sardus1970/JR_BLE_Gamepad/data/stripboard_top.png

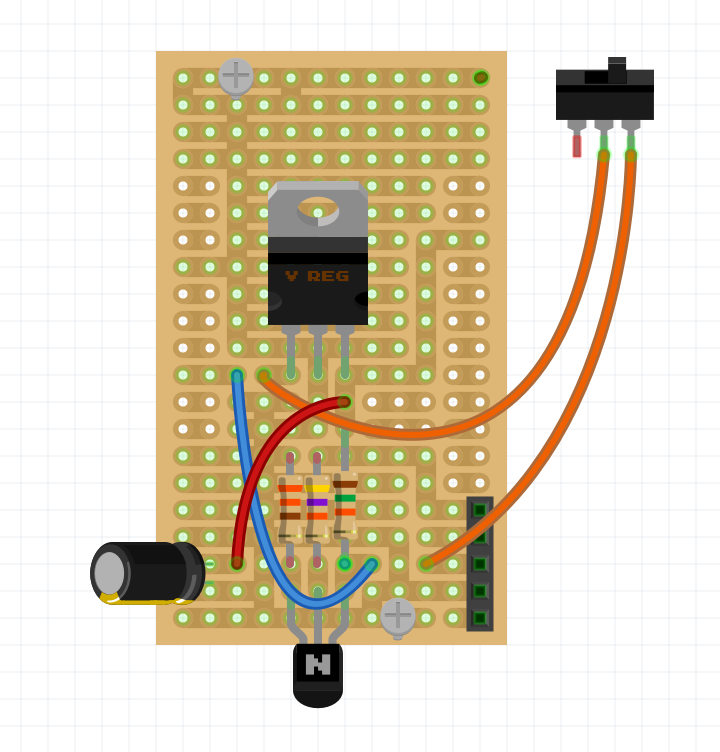
data/stripboard_top.png
